kim-xps12/tws_lp_jis60/docs/build_guide/images/asm_main_buttom_L.png

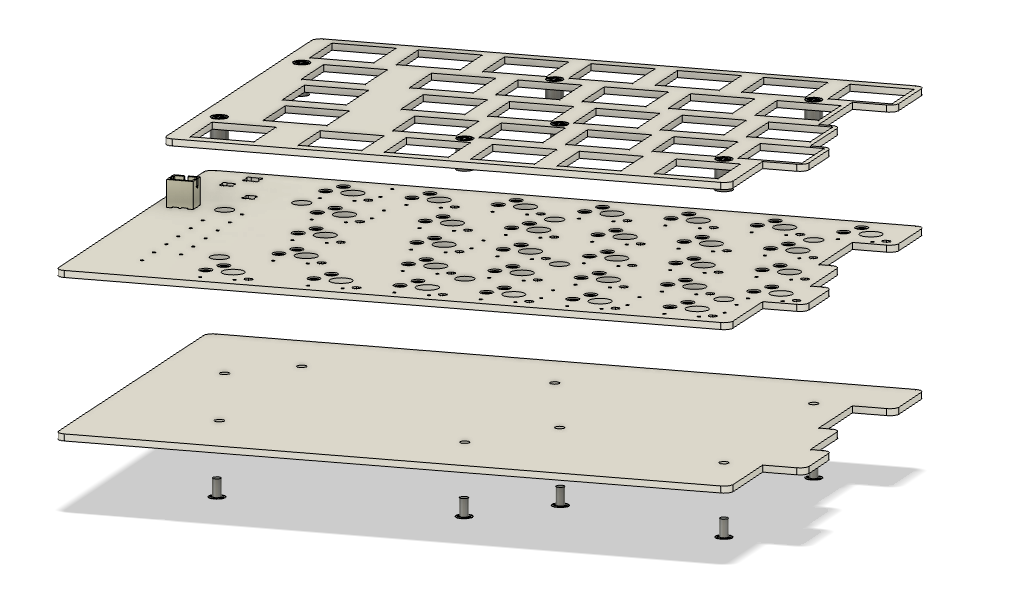
docs/build_guide/images/asm_main_buttom_L.png
