kim-xps12/tws_lp_jis60/docs/build_guide/images/ph_direction_before.jpeg

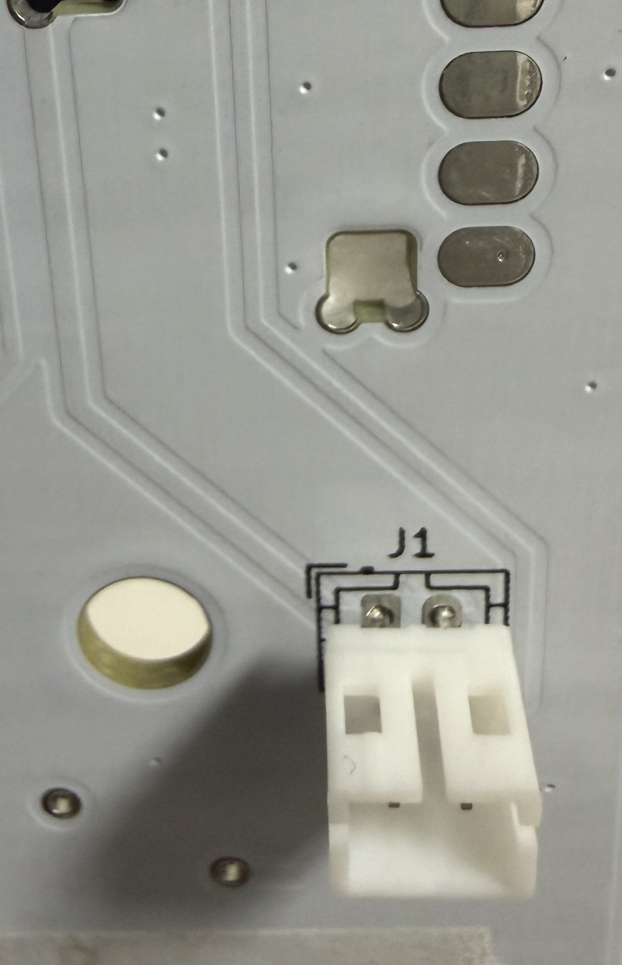
docs/build_guide/images/ph_direction_before.jpeg
