kim-xps12/tws_lp_jis60/docs/build_guide/images/set_bat_cover2.jpeg

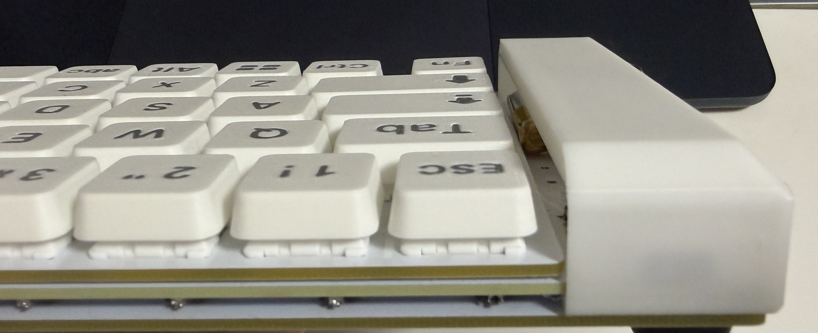
docs/build_guide/images/set_bat_cover2.jpeg
